Jorgeto0/FOBTool/Custom_Components/FOBtool_Custom/3dmodels/PN7160B1HN_C100E.stp

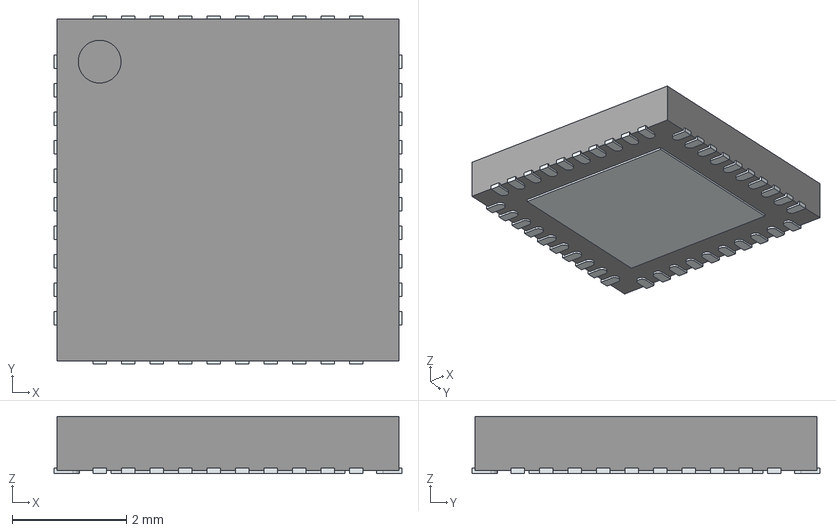
[picture p15: CAD file, 2026-10-05]
Custom_Components/FOBtool_Custom/3dmodels/PN7160B1HN_C100E.stp
6.10 x 6.10 x 1.00 mm
ThermalPin
PinsArrayLR
PinsArrayTB
