Jorgeto0/FOBTool/Custom_Components/FOBtool_Custom/3dmodels/MAX-M10N-10B.stp

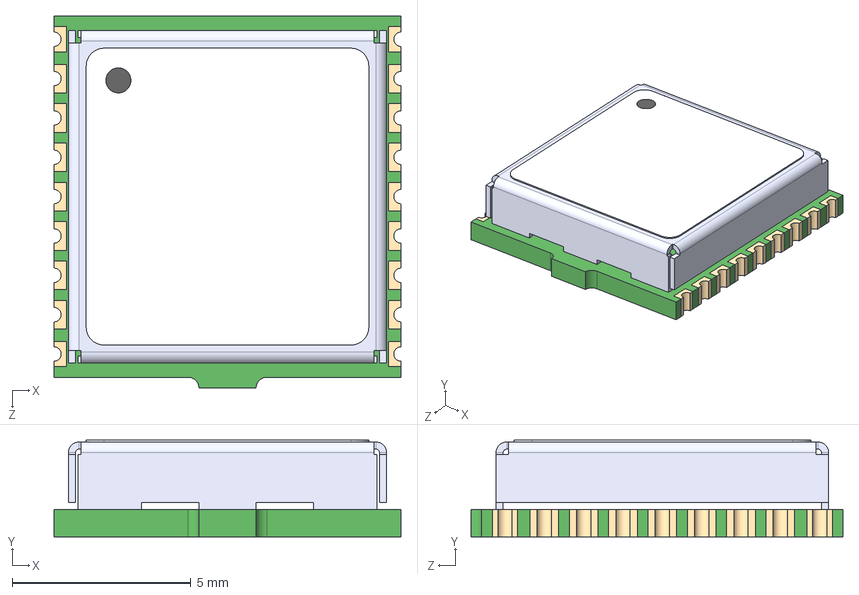
[picture p16: CAD file, 2026-10-05]
Custom_Components/FOBtool_Custom/3dmodels/MAX-M10N-10B.stp
9.70 x 2.70 x 10.4 mm
