Jorgeto0/FOBTool/Custom_Components/FOBtool_Custom/3dmodels/rpi_rp2350a.step

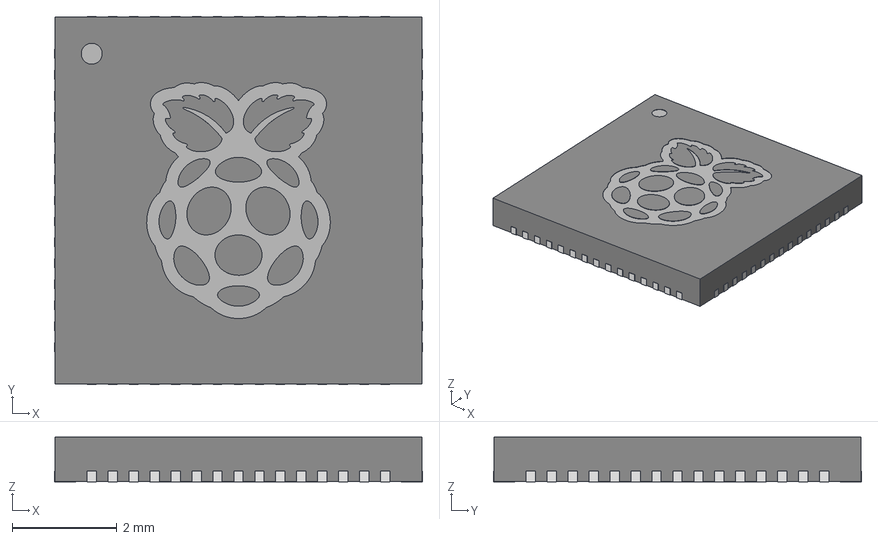
[picture p17: CAD file, 2026-09-17]
Custom_Components/FOBtool_Custom/3dmodels/rpi_rp2350a.step
7.02 x 7.02 x 0.85 mm
Package
EP
Pin1Indicator
Pins
Logo
