Jorgeto0/FOBTool/Custom_Components/FOBtool_Custom/3dmodels/SLP0603P2X3F_SEM.step

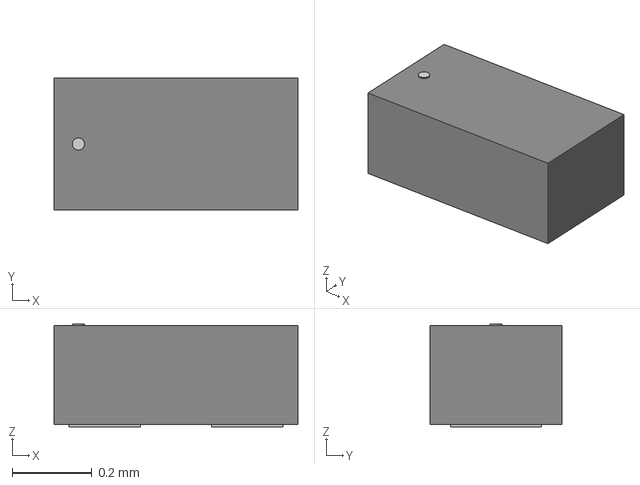
[picture p18: CAD file, 2026-09-11]
Custom_Components/FOBtool_Custom/3dmodels/SLP0603P2X3F_SEM.step
0.61 x 0.33 x 0.257 mm
