Jorgeto0/FOBTool/Custom_Components/FOBtool_Custom/3dmodels/BGS13SN8E6327XTSA1.stp

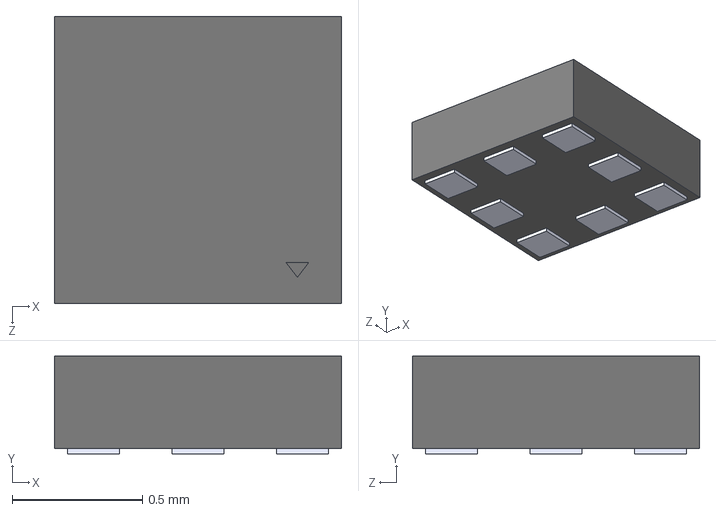
[picture p19: CAD file, 2026-09-11]
Custom_Components/FOBtool_Custom/3dmodels/BGS13SN8E6327XTSA1.stp
1.10 x 0.375 x 1.10 mm
