Jorgeto0/FOBTool/Custom_Components/FOBtool_Custom/3dmodels/EEFTX0J121RF.step

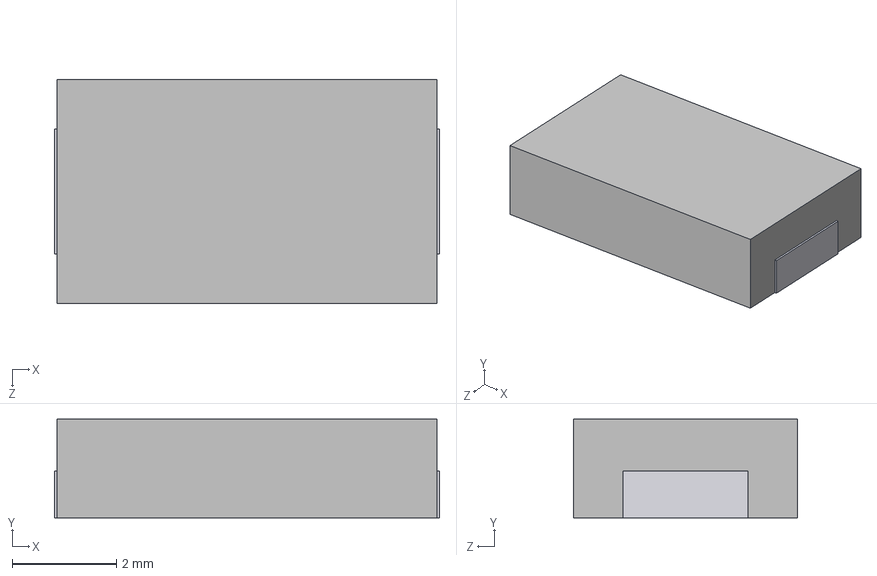
[picture p20: CAD file, 2026-09-11]
Custom_Components/FOBtool_Custom/3dmodels/EEFTX0J121RF.step
7.40 x 1.90 x 4.30 mm
SX2.0^GX_SX_CX_HX(2)_EEFKX0D471RB
??1^GX_SX_CX_HX(2)_EEFKX0D471RB
??2^GX_SX_CX_HX(2)_EEFKX0D471RB
