Jorgeto0/FOBTool/Custom_Components/FOBtool_Custom/3dmodels/LQH44PN150MPRL.step

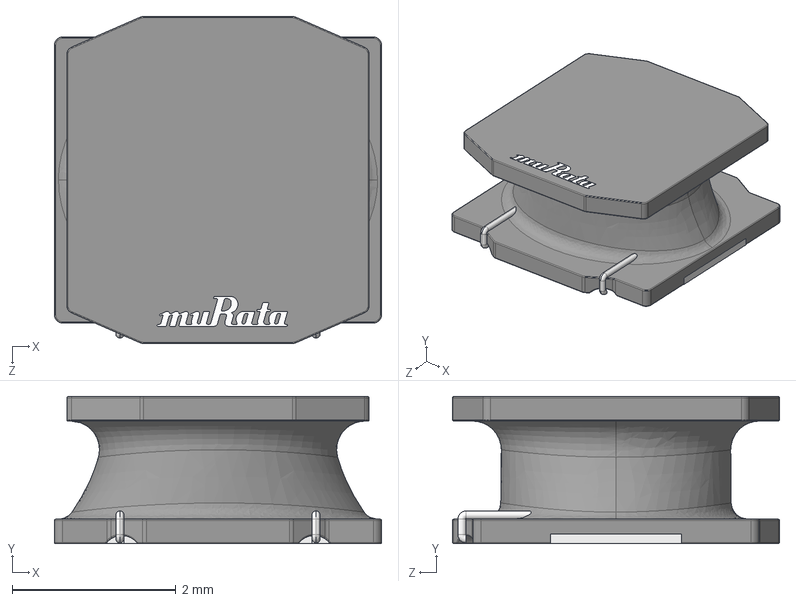
[picture p21: CAD file, 2026-09-11]
Custom_Components/FOBtool_Custom/3dmodels/LQH44PN150MPRL.step
4.00 x 1.80 x 4.00 mm
logo
terminals
terminal wire
