Jorgeto0/FOBTool/Custom_Components/FOBtool_Custom/3dmodels/AOTA-B201610S3R3-101-T--3DModel-STEP-510211.STEP

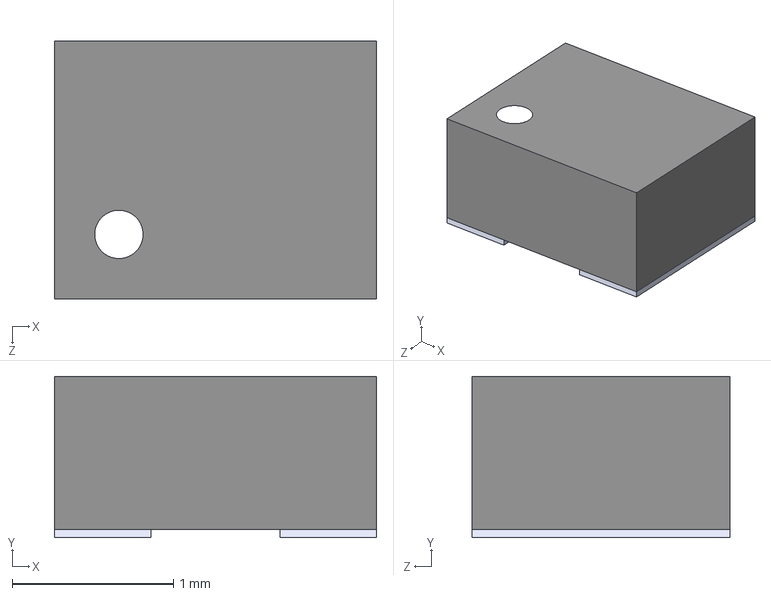
[picture p22: CAD file, 2026-09-11]
Custom_Components/FOBtool_Custom/3dmodels/AOTA-B201610S3R3-101-T--3DModel-STEP-510211.STEP
2.00 x 1.00 x 1.60 mm
