Jorgeto0/FOBTool/Custom_Components/FOBtool_Custom/3dmodels/CPH3225A.step

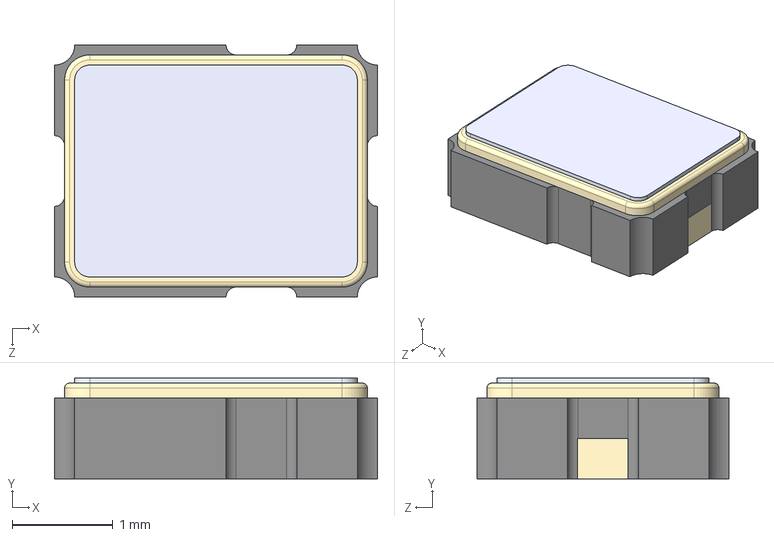
[picture p23: CAD file, 2026-09-11]
Custom_Components/FOBtool_Custom/3dmodels/CPH3225A.step
3.20 x 1.00 x 2.50 mm
