Jorgeto0/FOBTool/Custom_Components/FOBtool_Custom/3dmodels/EEFLR0J680R.step

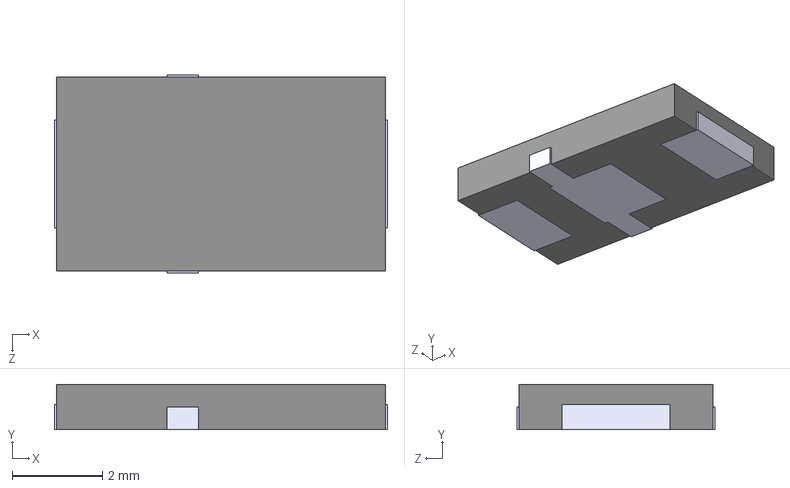
[picture p24: CAD file, 2026-09-11]
Custom_Components/FOBtool_Custom/3dmodels/EEFLR0J680R.step
7.40 x 1.00 x 4.40 mm
