Jorgeto0/FOBTool/Custom_Components/FOBtool_Custom/3dmodels/BD0826J50200AHF.stp

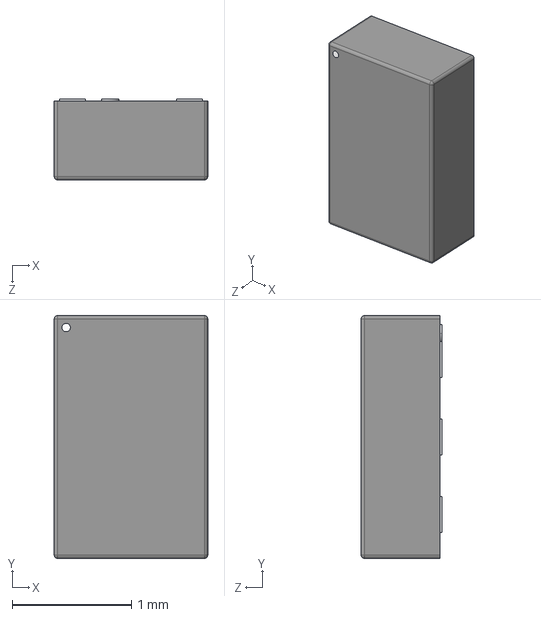
[picture p25: CAD file, 2026-09-11]
Custom_Components/FOBtool_Custom/3dmodels/BD0826J50200AHF.stp
1.29 x 2.04 x 0.68 mm
