Jorgeto0/FOBTool/Custom_Components/FOBtool_Custom/3dmodels/PEC11R-4215F-S0024--3DModel-STEP-56544.STEP

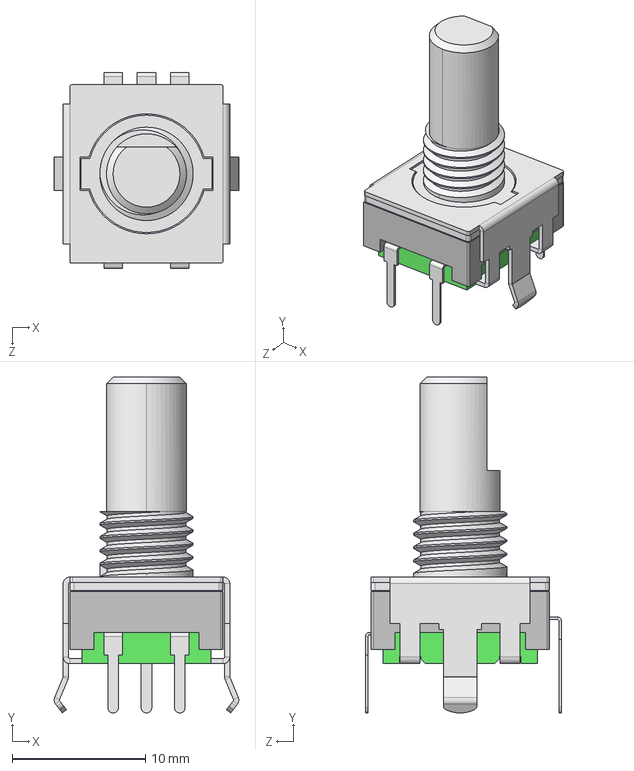
[picture p26: CAD file, 2026-09-10]
Custom_Components/FOBtool_Custom/3dmodels/PEC11R-4215F-S0024--3DModel-STEP-56544.STEP
13.9 x 25.2 x 14.7 mm
