Jorgeto0/FOBTool/Custom_Components/FOBtool_Custom/3dmodels/UWA.01_Web.STEP

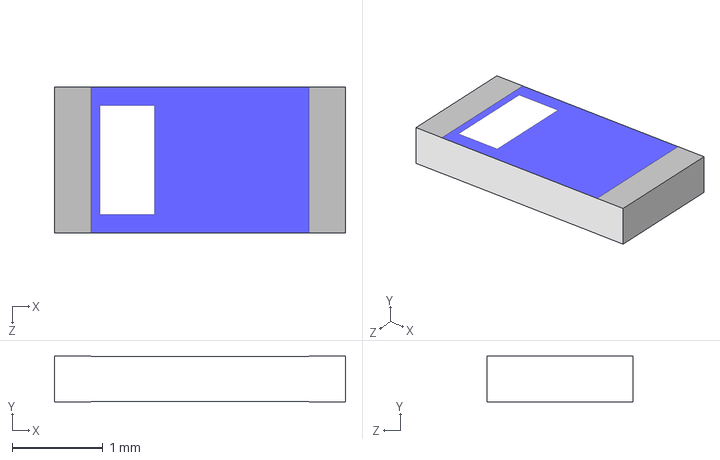
[picture p27: CAD file, 2026-09-10]
Custom_Components/FOBtool_Custom/3dmodels/UWA.01_Web.STEP
3.20 x 0.502 x 1.60 mm
